BroncoSpace-BILLEE/BILLEE-Hardware-2025-2026/mercury-1/mercury-1.kicad_sch

## KiCad design mercury-1/mercury-1.kicad_sch (2026-02-26, an earlier design)

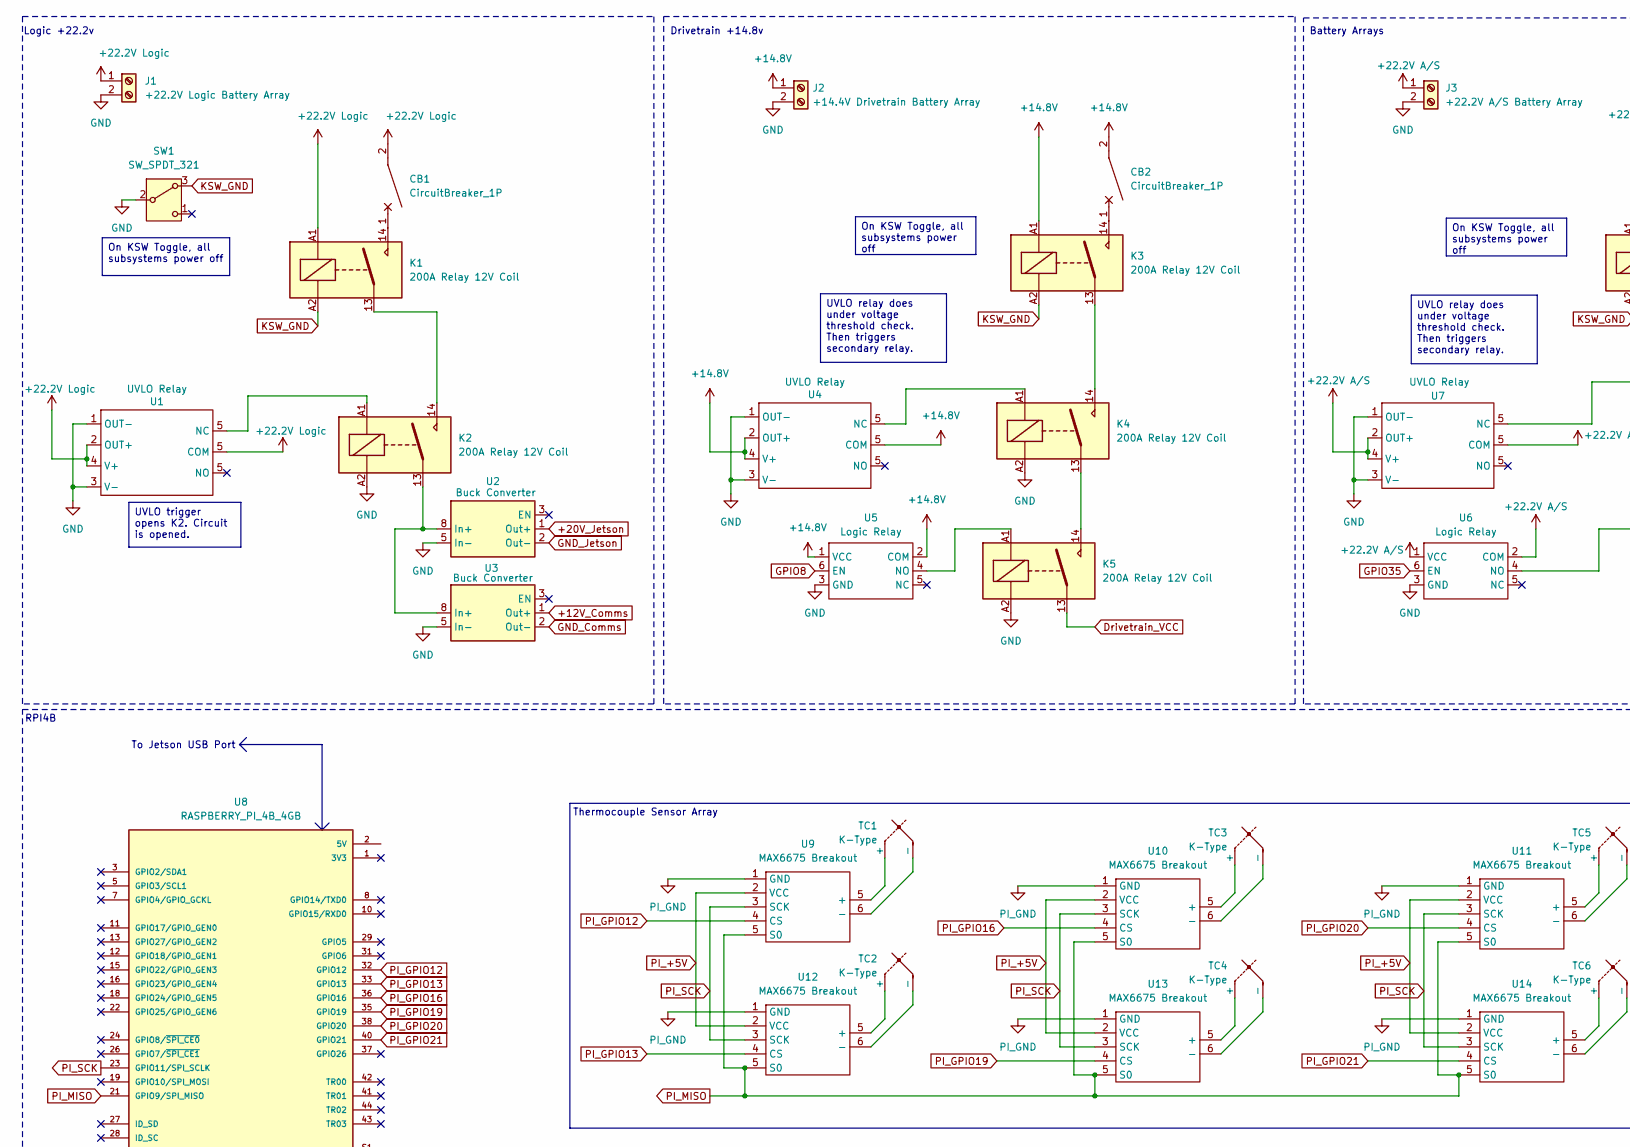
[picture p3: schematic mercury-1.kicad_sch, part in row 1, column 1]

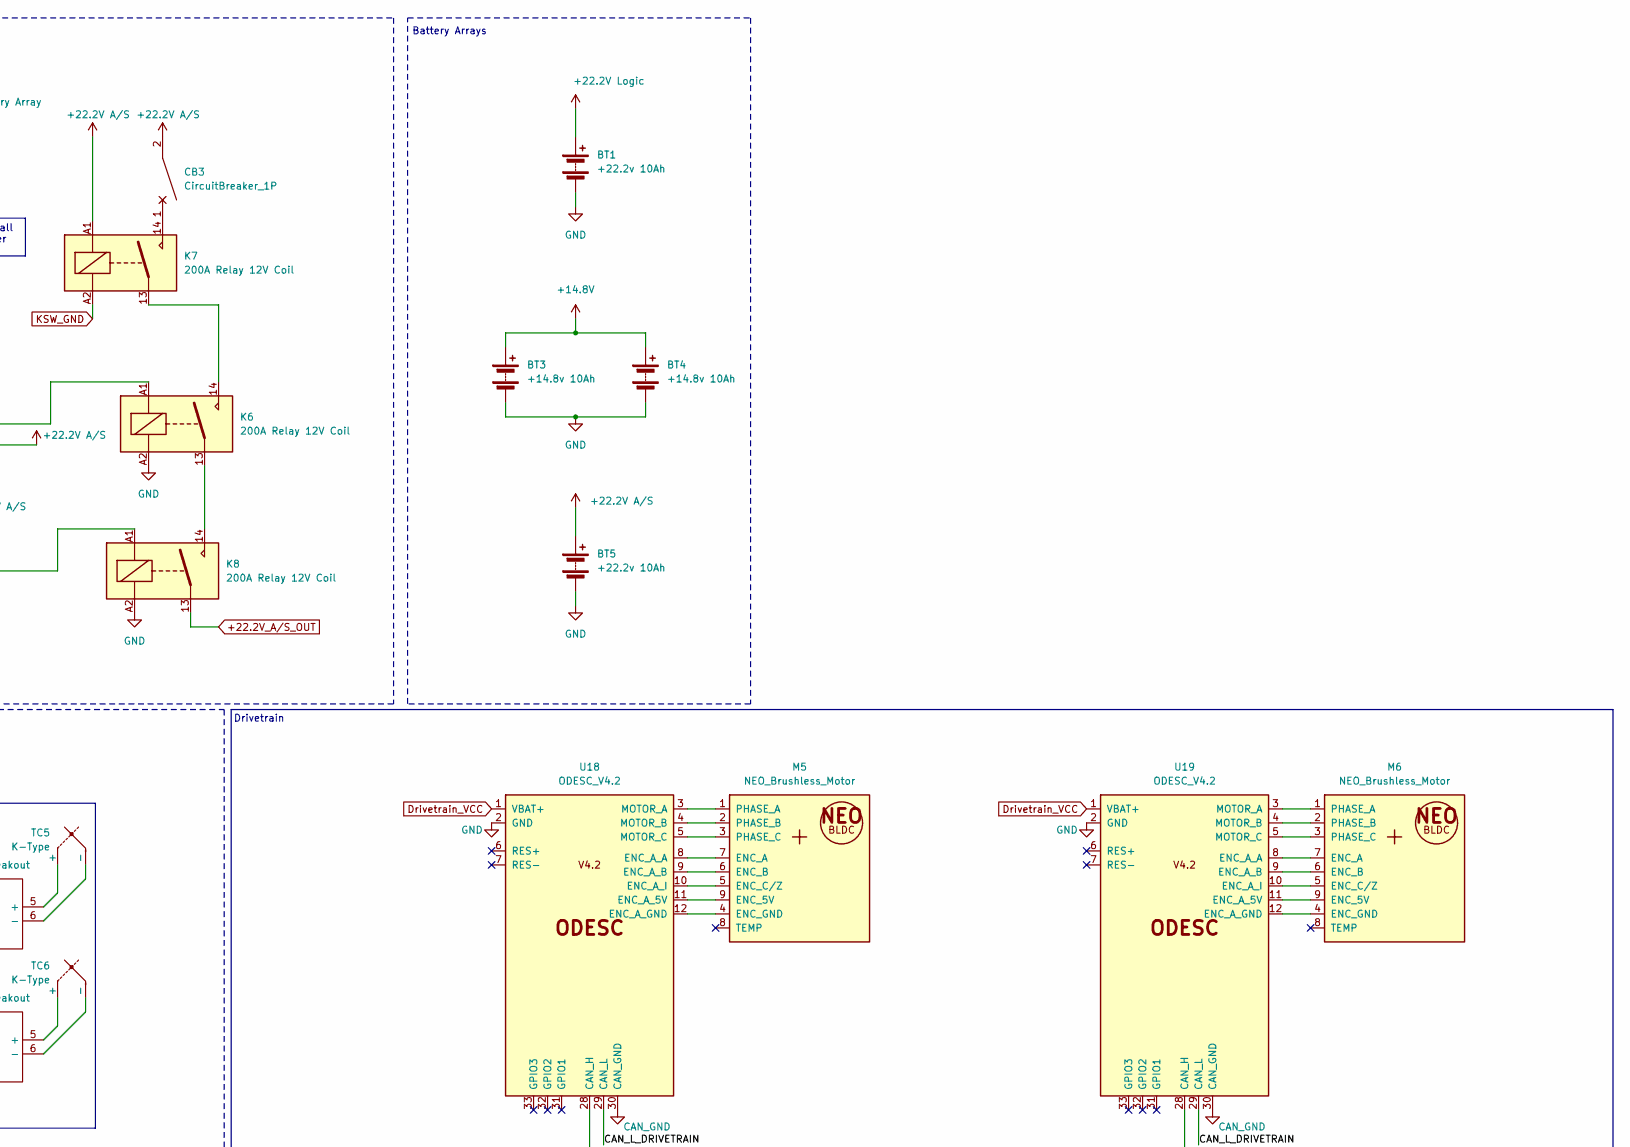
[picture p4: schematic mercury-1.kicad_sch, part in row 1, column 2]

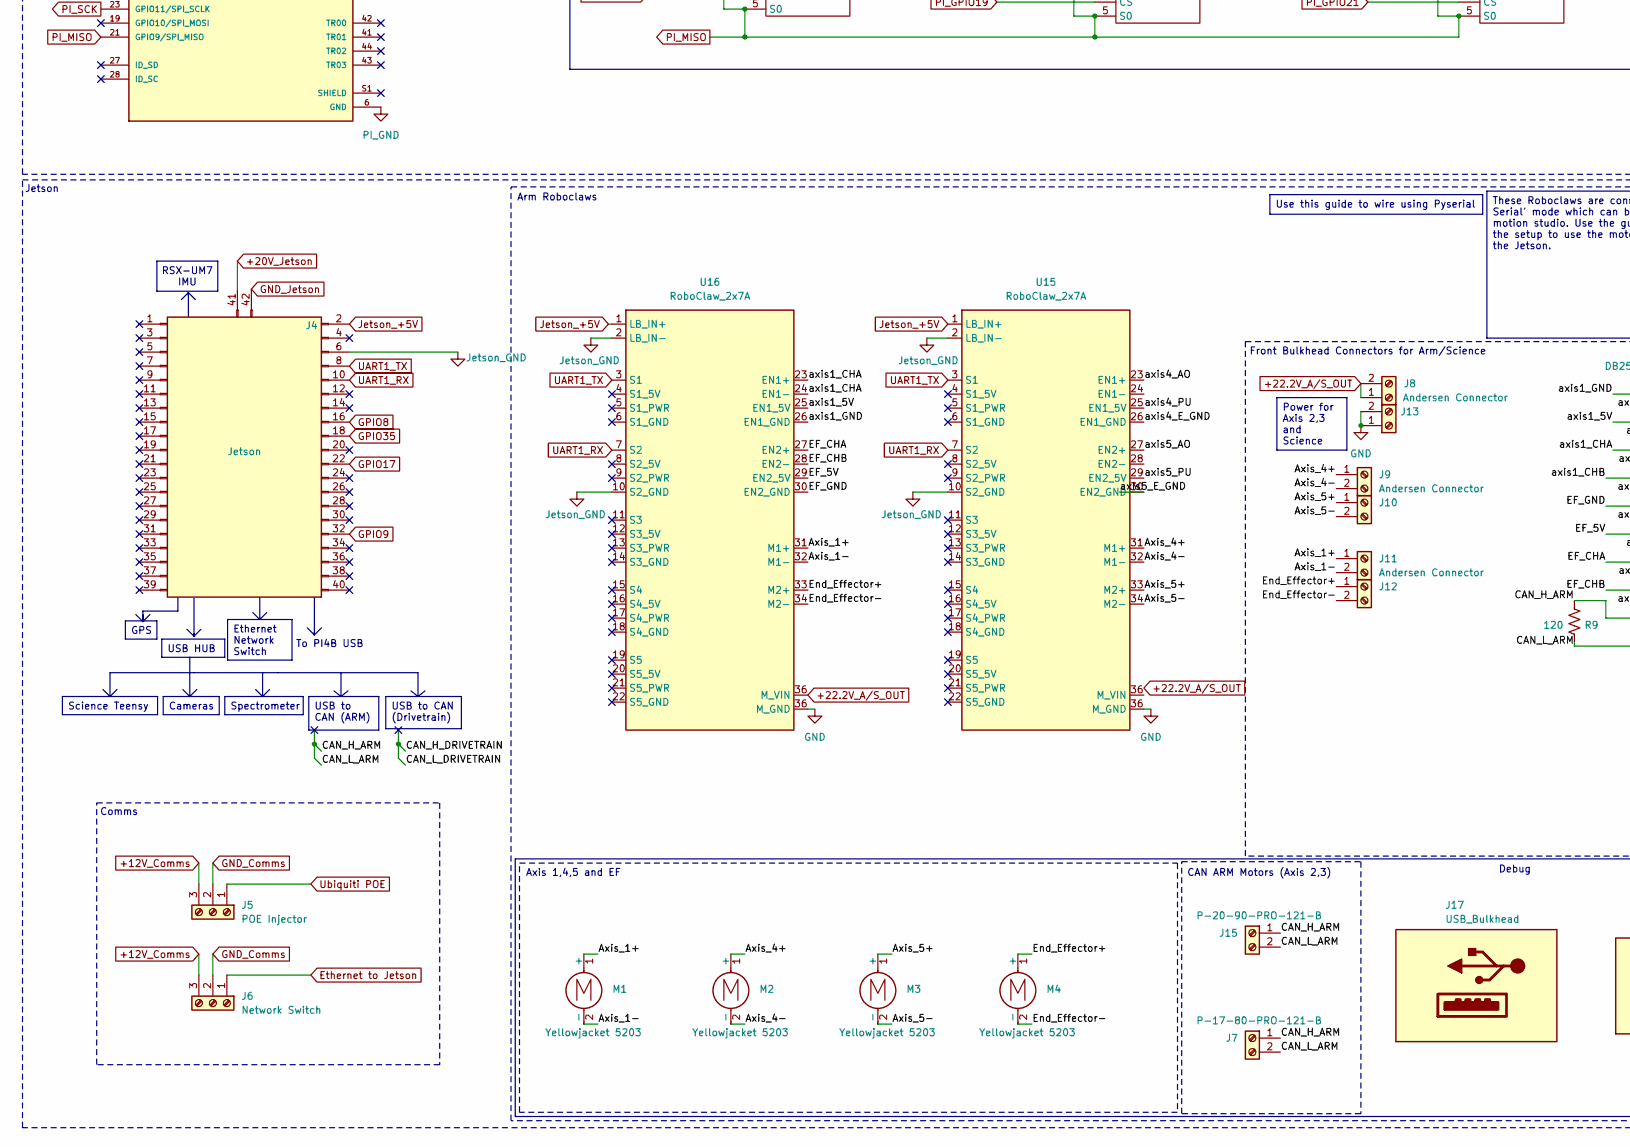
[picture p5: schematic mercury-1.kicad_sch, part in row 2, column 1]

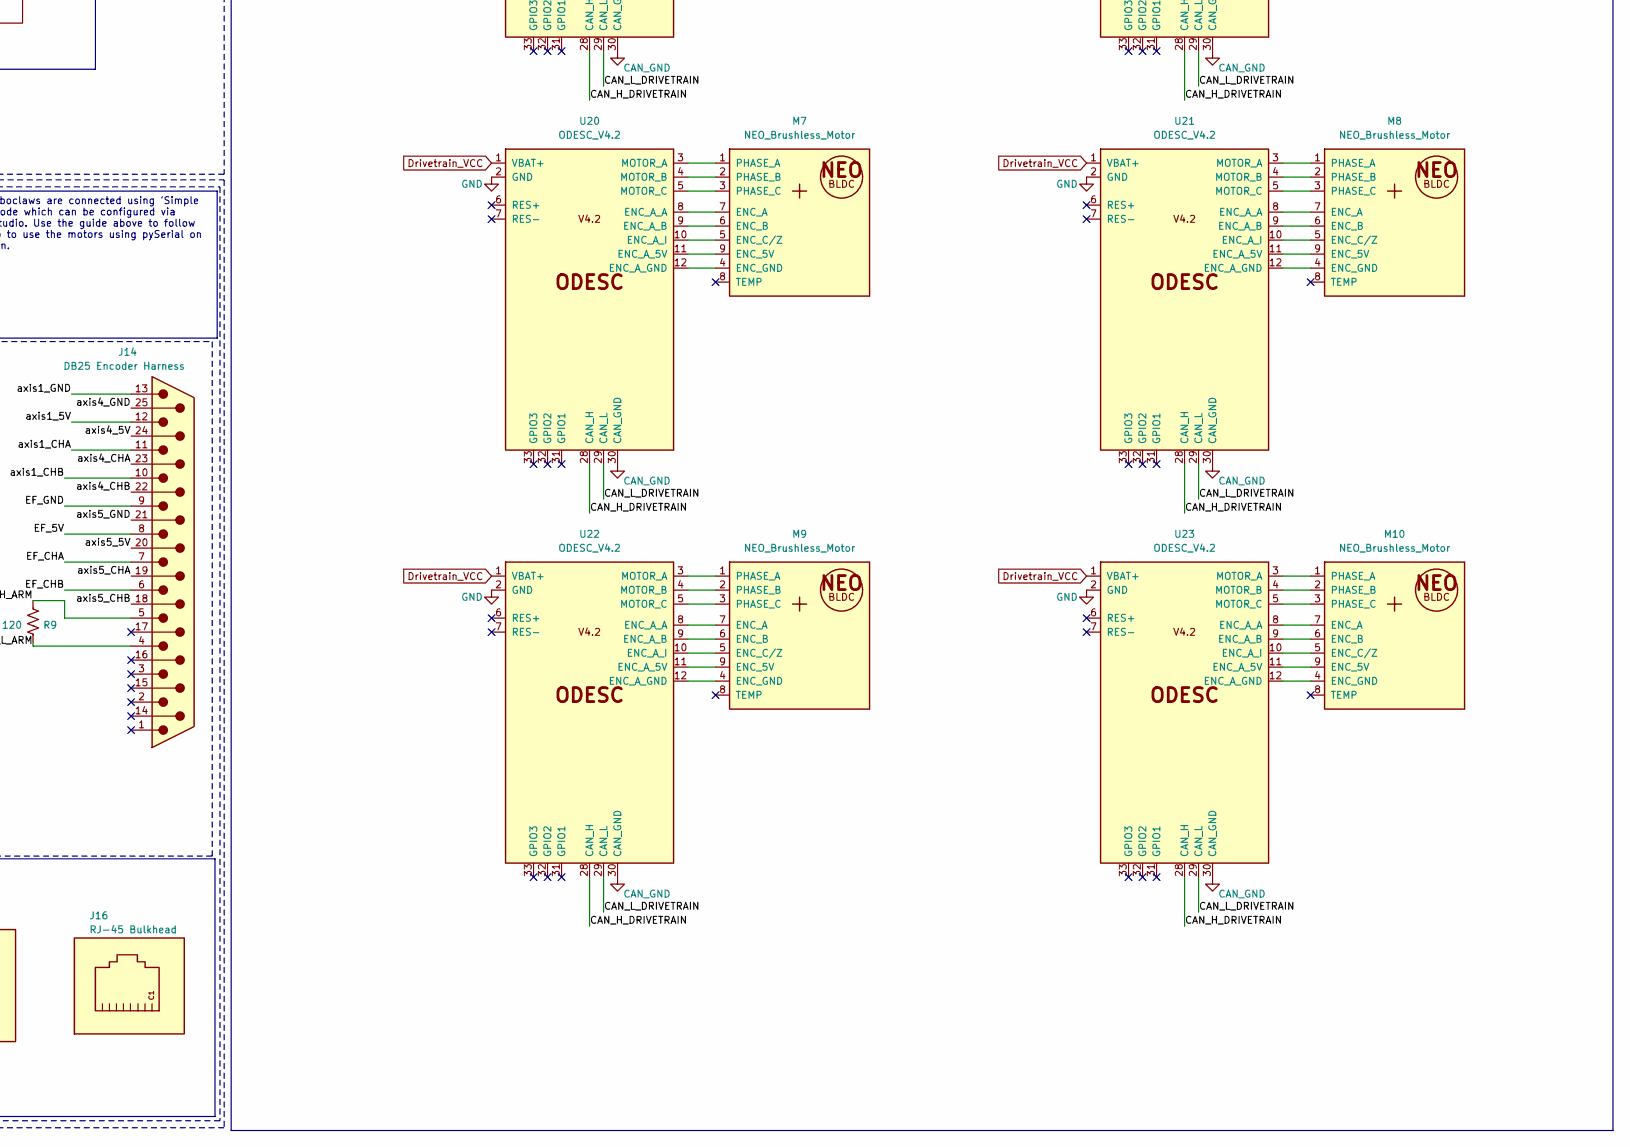
[picture p6: schematic mercury-1.kicad_sch, part in row 2, column 2]

Parts:
BT1, BT5: +22.2v 10Ah
BT3, BT4: +14.8v 10Ah
CB1, CB2, CB3: CircuitBreaker_1P
J1: +22.2V Logic Battery Array
J2: +14.4V Drivetrain Battery Array
J3: +22.2V A/S Battery Array
J4: Jetson
J5: POE Injector
J6: Network Switch
J7: P-17-80-PRO-121-B
J8, J9, J10, J11, J12, J13: Andersen Connector
J14: DB25 Encoder Harness
J15: P-20-90-PRO-121-B
J16: RJ-45 Bulkhead; RJ45_Bel_V895-1001-AW_Vertical
J17: USB_Bulkhead
K1, K2, K3, K4, K5, K6, K7, K8: 200A Relay 12V Coil
M1, M2, M3, M4: Yellowjacket 5203
M5, M6, M7, M8, M9, M10: NEO_Brushless_Motor
R9: 120
SW1: SW_SPDT_321
TC1, TC2, TC3, TC4, TC5, TC6: K-Type
U1, U4, U7: UVLO Relay
U2, U3: Buck Converter; HTSOP-8-1EP_3.9x4.9mm_P1.27mm_EP2.4x3.2mm
U5, U6: Logic Relay
U8: RASPBERRY_PI_4B_4GB; MODULE_RASPBERRY_PI_4B_4GB; PARTREV 4
U9, U10, U11, U12, U13, U14: MAX6675 Breakout
U15, U16: RoboClaw_2x7A
U18, U19, U20, U21, U22, U23: ODESC_V4.2

Connections:
+12V_Comms: J5.3, J6.3, U3.1 (Out+)
+14.8V: BT3.1 (+), BT4.1 (+), CB2.2, J2.1, K3.A1, U4.2 (OUT+), U4.4 (V+), U4.5 (NC), U5.1 (VCC), U5.2 (COM)
+20V_Jetson: J4.41, U2.1 (Out+)
+22.2V A/S: BT5.1 (+), CB3.2, J3.1, K7.A1, U6.1 (VCC), U6.2 (COM), U7.2 (OUT+), U7.4 (V+), U7.5 (NC)
+22.2V Logic: BT1.1 (+), CB1.2, J1.1, K1.A1, U1.2 (OUT+), U1.4 (V+), U1.5 (NC)
+22.2V_A/S_OUT: J8.1, J8.2, K8.13, U16.36 (M_VIN)
Axis_1+: J11.1, M1.1 (+), U16.31 (M1+)
Axis_1-: J11.2, M1.2 (-), U16.32 (M1-)
Axis_4+: J9.1, M2.1 (+), U15.31 (M1+)
Axis_4-: J9.2, M2.2 (-), U15.32 (M1-)
Axis_5+: J10.1, M3.1 (+), U15.33 (M2+)
Axis_5-: J10.2, M3.2 (-), U15.34 (M2-)
CAN_GND: U18.30 (CAN_GND), U19.30 (CAN_GND), U20.30 (CAN_GND), U21.30 (CAN_GND), U22.30 (CAN_GND), U23.30 (CAN_GND)
CAN_H_ARM: J7.1, J7.2, J14.4, J14.5, J15.1, J15.2, R9.1, R9.2
CAN_H_DRIVETRAIN: U18.28 (CAN_H), U18.29 (CAN_L), U19.28 (CAN_H), U19.29 (CAN_L), U20.28 (CAN_H), U20.29 (CAN_L), U21.28 (CAN_H), U21.29 (CAN_L), U22.28 (CAN_H), U22.29 (CAN_L), U23.28 (CAN_H), U23.29 (CAN_L)
Drivetrain_VCC: K5.13, U18.1 (VBAT+), U19.1 (VBAT+), U20.1 (VBAT+), U21.1 (VBAT+), U22.1 (VBAT+), U23.1 (VBAT+)
EF_5V: J14.8, U16.29 (EN2_5V)
EF_CHA: J14.7, U16.27 (EN2+)
EF_CHB: J14.6, U16.28 (EN2-)
EF_GND: J14.9, U16.30 (EN2_GND)
End_Effector+: J12.1, M4.1 (+), U16.33 (M2+)
End_Effector-: J12.2, M4.2 (-), U16.34 (M2-)
Ethernet to Jetson: J6.1
GND: BT1.2 (-), BT3.2 (-), BT4.2 (-), BT5.2 (-), J1.2, J2.2, J3.2, J13.1, J13.2, K2.A2, K4.A2, K5.A2, K6.A2, K8.A2, SW1.2 (B), U1.1 (OUT-), U1.3 (V-), U2.5 (In-), U3.5 (In-), U4.1 (OUT-), U4.3 (V-), U5.3 (GND), U6.3 (GND), U7.1 (OUT-), U7.3 (V-), U15.36 (M_VIN), U16.36 (M_VIN), U18.2 (GND), U19.2 (GND), U20.2 (GND), U21.2 (GND), U22.2 (GND), U23.2 (GND)
GND_Comms: J5.2, J6.2, U3.2 (Out-)
GND_Jetson: J4.42, U2.2 (Out-)
GPIO8: J4.16, U5.6 (EN)
GPIO9: J4.32
GPIO17: J4.22
GPIO35: J4.18, U6.6 (EN)
Jetson_+5V: J4.2, U15.1 (LB_IN+), U16.1 (LB_IN+)
Jetson_GND: J4.6, U15.2 (LB_IN-), U15.10 (S2_GND), U16.2 (LB_IN-), U16.10 (S2_GND)
KSW_GND: K1.A2, K3.A2, K7.A2, SW1.3 (A)
unnamed: CB1.1, K1.14
unnamed: CB2.1, K3.14
unnamed: CB3.1, K7.14
unnamed: K1.13, K2.14
unnamed: K2.13, U2.8 (In+), U3.8 (In+)
unnamed: K2.A1, U1.5 (NC)
unnamed: K3.13, K4.14
unnamed: K4.13, K5.14
unnamed: K4.A1, U4.5 (NC)
unnamed: K5.A1, U5.4 (NO)
unnamed: K6.13, K8.14
unnamed: K6.14, K7.13
unnamed: K6.A1, U7.5 (NC)
unnamed: K8.A1, U6.4 (NO)
unnamed: M5.1 (PHASE_A), U18.3 (MOTOR_A)
unnamed: M5.2 (PHASE_B), U18.4 (MOTOR_B)
unnamed: M5.3 (PHASE_C), U18.5 (MOTOR_C)
unnamed: M5.4 (ENC_GND), U18.12 (ENC_A_GND)
unnamed: M5.5 (ENC_C/Z), U18.10 (ENC_A_I)
unnamed: M5.6 (ENC_B), U18.9 (ENC_A_B)
unnamed: M5.7 (ENC_A), U18.8 (ENC_A_A)
unnamed: M5.9 (ENC_5V), U18.11 (ENC_A_5V)
unnamed: M6.1 (PHASE_A), U19.3 (MOTOR_A)
unnamed: M6.2 (PHASE_B), U19.4 (MOTOR_B)
unnamed: M6.3 (PHASE_C), U19.5 (MOTOR_C)
unnamed: M6.4 (ENC_GND), U19.12 (ENC_A_GND)
unnamed: M6.5 (ENC_C/Z), U19.10 (ENC_A_I)
unnamed: M6.6 (ENC_B), U19.9 (ENC_A_B)
unnamed: M6.7 (ENC_A), U19.8 (ENC_A_A)
unnamed: M6.9 (ENC_5V), U19.11 (ENC_A_5V)
unnamed: M7.1 (PHASE_A), U20.3 (MOTOR_A)
unnamed: M7.2 (PHASE_B), U20.4 (MOTOR_B)
unnamed: M7.3 (PHASE_C), U20.5 (MOTOR_C)
unnamed: M7.4 (ENC_GND), U20.12 (ENC_A_GND)
unnamed: M7.5 (ENC_C/Z), U20.10 (ENC_A_I)
unnamed: M7.6 (ENC_B), U20.9 (ENC_A_B)
unnamed: M7.7 (ENC_A), U20.8 (ENC_A_A)
unnamed: M7.9 (ENC_5V), U20.11 (ENC_A_5V)
unnamed: M8.1 (PHASE_A), U21.3 (MOTOR_A)
unnamed: M8.2 (PHASE_B), U21.4 (MOTOR_B)
unnamed: M8.3 (PHASE_C), U21.5 (MOTOR_C)
unnamed: M8.4 (ENC_GND), U21.12 (ENC_A_GND)
unnamed: M8.5 (ENC_C/Z), U21.10 (ENC_A_I)
unnamed: M8.6 (ENC_B), U21.9 (ENC_A_B)
unnamed: M8.7 (ENC_A), U21.8 (ENC_A_A)
unnamed: M8.9 (ENC_5V), U21.11 (ENC_A_5V)
unnamed: M9.1 (PHASE_A), U22.3 (MOTOR_A)
unnamed: M9.2 (PHASE_B), U22.4 (MOTOR_B)
unnamed: M9.3 (PHASE_C), U22.5 (MOTOR_C)
unnamed: M9.4 (ENC_GND), U22.12 (ENC_A_GND)
unnamed: M9.5 (ENC_C/Z), U22.10 (ENC_A_I)
unnamed: M9.6 (ENC_B), U22.9 (ENC_A_B)
unnamed: M9.7 (ENC_A), U22.8 (ENC_A_A)
unnamed: M9.9 (ENC_5V), U22.11 (ENC_A_5V)
unnamed: M10.1 (PHASE_A), U23.3 (MOTOR_A)
unnamed: M10.2 (PHASE_B), U23.4 (MOTOR_B)
unnamed: M10.3 (PHASE_C), U23.5 (MOTOR_C)
unnamed: M10.4 (ENC_GND), U23.12 (ENC_A_GND)
unnamed: M10.5 (ENC_C/Z), U23.10 (ENC_A_I)
unnamed: M10.6 (ENC_B), U23.9 (ENC_A_B)
unnamed: M10.7 (ENC_A), U23.8 (ENC_A_A)
unnamed: M10.9 (ENC_5V), U23.11 (ENC_A_5V)
unnamed: TC1.1 (+), U9.5 (S0)
unnamed: TC1.2 (-), U9.6 (-)
unnamed: TC2.1 (+), U12.5 (S0)
unnamed: TC2.2 (-), U12.6 (-)
unnamed: TC3.1 (+), U10.5 (S0)
unnamed: TC3.2 (-), U10.6 (-)
unnamed: TC4.1 (+), U13.5 (S0)
unnamed: TC4.2 (-), U13.6 (-)
unnamed: TC5.1 (+), U11.5 (S0)
unnamed: TC5.2 (-), U11.6 (-)
unnamed: TC6.1 (+), U14.5 (S0)
unnamed: TC6.2 (-), U14.6 (-)
unnamed: U2.4 (GND), U2.6 (GND), U2.7 (GND), U2.9 (GND)
unnamed: U3.4 (GND), U3.6 (GND), U3.7 (GND), U3.9 (GND)
unnamed: U8.1 (3V3), U8.17 (3V3)
unnamed: U8.2 (5V), U8.4 (5V)
unnamed: U8.S1 (SHIELD), U8.S2 (SHIELD), U8.S3 (SHIELD), U8.S4 (SHIELD)
PI_+5V: U9.2 (VCC), U10.2 (VCC), U11.2 (VCC), U12.2 (VCC), U13.2 (VCC), U14.2 (VCC)
PI_GND: U8.6 (GND), U8.9 (GND), U8.14 (GND), U8.20 (GND), U8.25 (GND), U8.30 (GND), U8.34 (GND), U8.39 (GND), U9.1 (GND), U10.1 (GND), U11.1 (GND), U12.1 (GND), U13.1 (GND), U14.1 (GND)
PI_GPIO12: U8.32 (GPIO12), U9.4 (CS)
PI_GPIO13: U8.33 (GPIO13), U12.4 (CS)
PI_GPIO16: U8.36 (GPIO16), U10.4 (CS)
PI_GPIO19: U8.35 (GPIO19), U13.4 (CS)
PI_GPIO20: U8.38 (GPIO20), U11.4 (CS)
PI_GPIO21: U8.40 (GPIO21), U14.4 (CS)
PI_MISO: U8.21 (GPIO9/SPI_MISO), U9.5 (S0), U10.5 (S0), U11.5 (S0), U12.5 (S0), U13.5 (S0), U14.5 (S0)
PI_SCK: U8.23 (GPIO11/SPI_SCLK), U9.3 (SCK), U10.3 (SCK), U11.3 (SCK), U12.3 (SCK), U13.3 (SCK), U14.3 (SCK)
UART1_RX: J4.10, U15.7 (S2), U16.7 (S2)
UART1_TX: J4.8, U15.3 (S1), U16.3 (S1)
Ubiquiti POE: J5.1
axis1_5V: J14.12, U16.25 (EN1_5V)
axis1_CHA: J14.11, U16.23 (EN1+), U16.24 (EN1-)
axis1_CHB: J14.10
axis1_GND: J14.13, U16.26 (EN1_GND)
axis4_5V: J14.24
axis4_AO: U15.23 (EN1+)
axis4_CHA: J14.23
axis4_CHB: J14.22
axis4_E_GND: U15.26 (EN1_GND)
axis4_GND: J14.25
axis4_PU: U15.25 (EN1_5V)
axis5_5V: J14.20
axis5_AO: U15.27 (EN2+)
axis5_CHA: J14.19
axis5_CHB: J14.18
axis5_E_GND: U15.30 (EN2_GND)
axis5_GND: J14.21
axis5_PU: U15.29 (EN2_5V)

Notes on the sheet:
To PI4B USB
Battery Arrays
Debug
Comms
CAN ARM Motors (Axis 2,3)
Axis 1,4,5 and EF
To Jetson USB Port
Thermocouple Sensor Array
Jetson
Drivetrain
Logic +22.2v
Drivetrain +14.8v
RPI4B
Front Bulkhead Connectors for Arm/Science
Arm Roboclaws
On KSW Toggle, all subsystems power off
Spectrometer
UVLO trigger opens K2. Circuit is opened.
RSX-UM7 IMU
USB to CAN (Drivetrain)
UVLO relay does under voltage threshold check. Then triggers secondary relay.
Ethernet Network Switch
USB HUB
GPS
Power for Axis 2,3 and Science
These Roboclaws are connected using 'Simple Serial' mode which can be configured via motion studio. Use the guide above to follow the setup to use the motors using pySerial on the Jetson.
Cameras
Science Teensy
Use this guide to wire using Pyserial
USB to CAN (ARM)
