BroncoSpace-BILLEE/BILLEE-Hardware-2025-2026/mercury-1/science.kicad_sch

## KiCad design mercury-1/science.kicad_sch (2026-02-27, an earlier design)

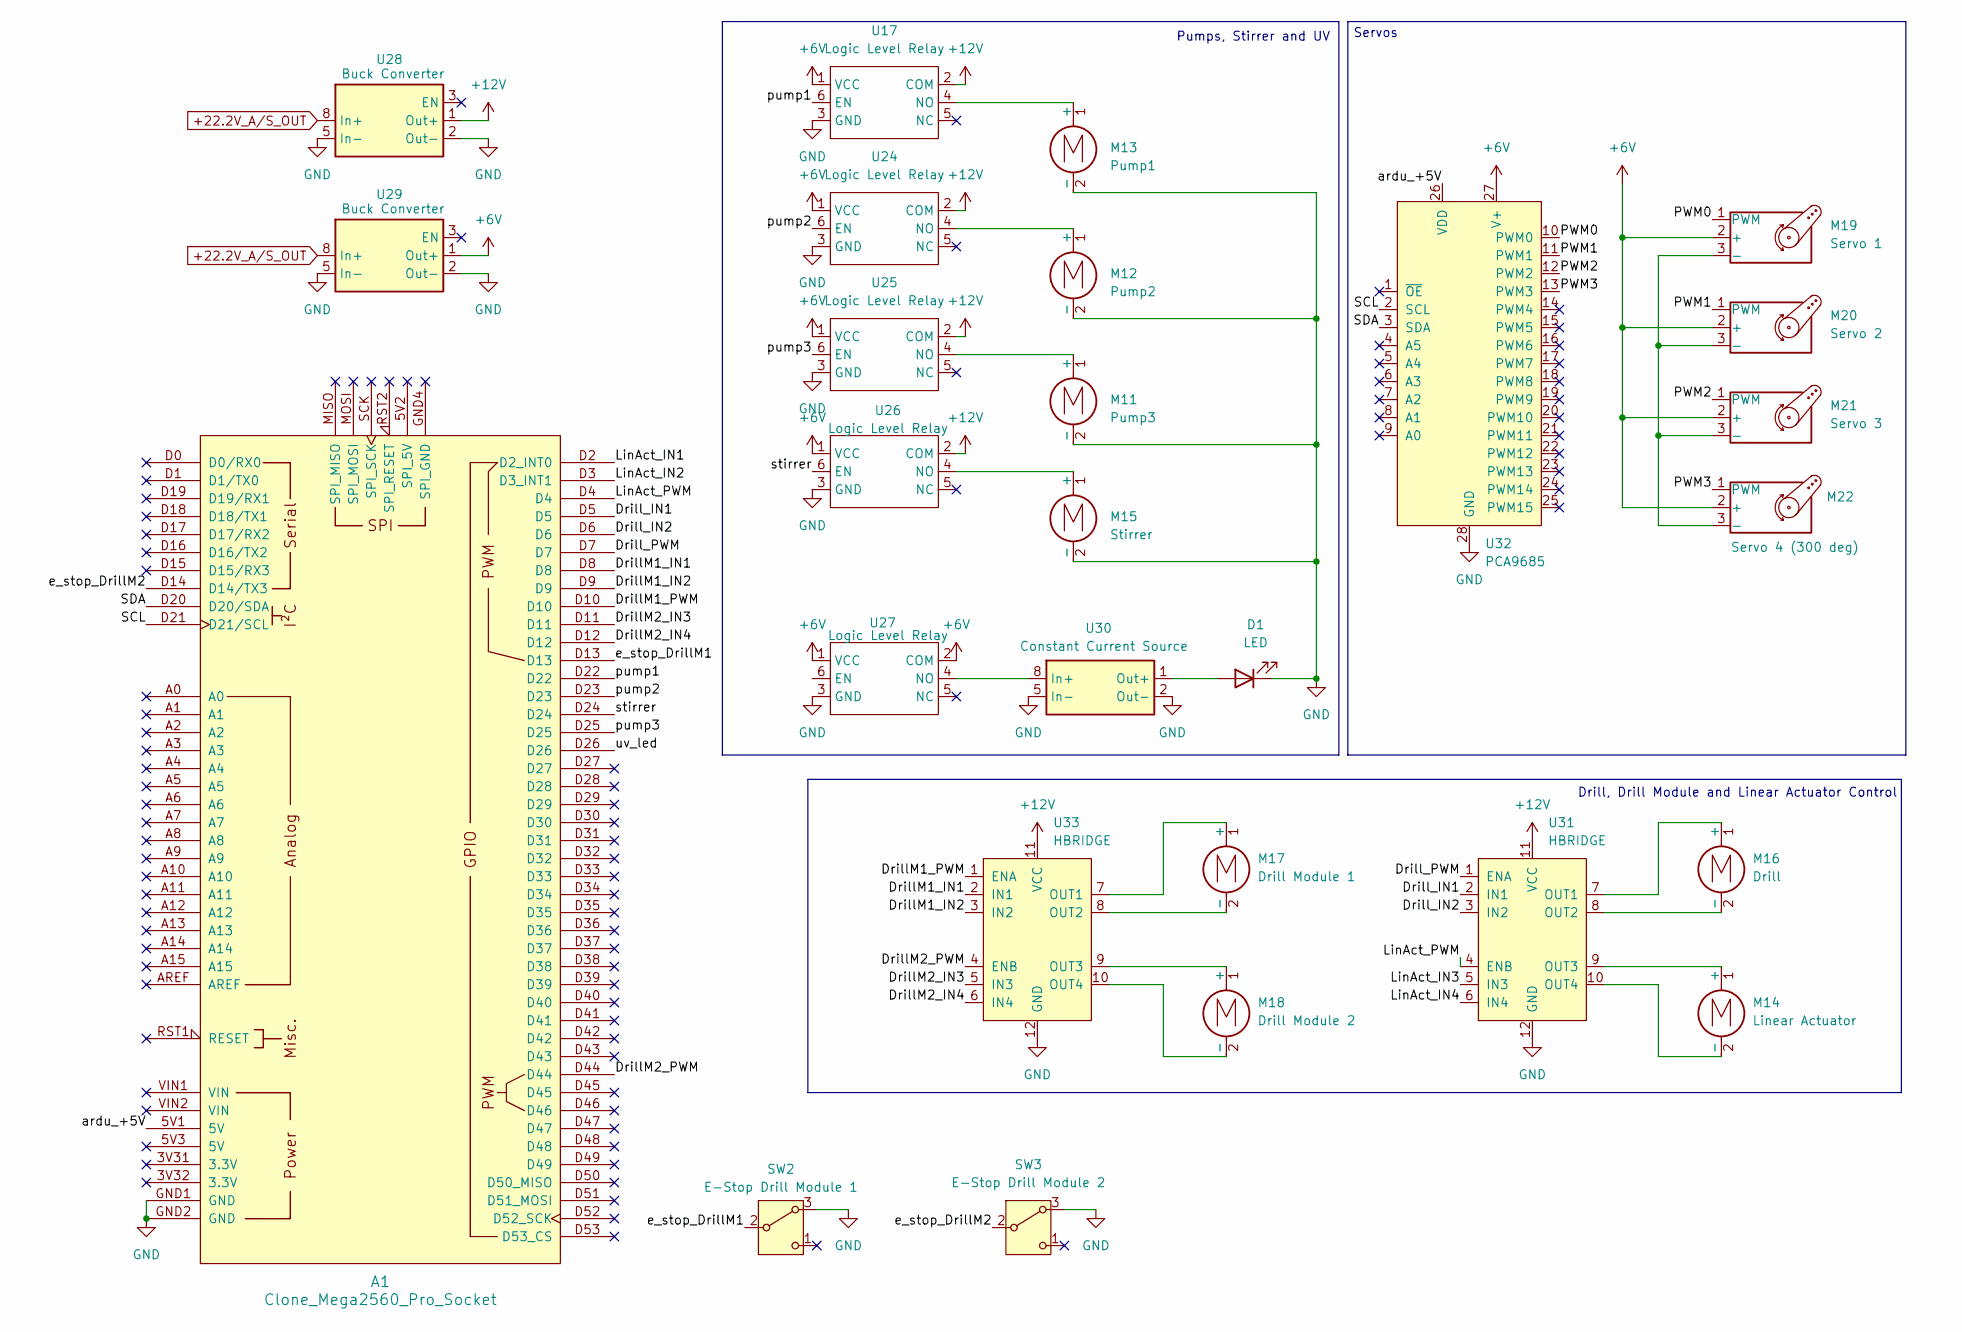
[picture p7: schematic science.kicad_sch]

Parts:
A1: Clone_Mega2560_Pro_Socket
D1: LED
M11: Pump3
M12: Pump2
M13: Pump1
M14: Linear Actuator
M15: Stirrer
M16: Drill
M17: Drill Module 1
M18: Drill Module 2
M19: Servo 1
M20: Servo 2
M21: Servo 3
M22: Servo 4 (300 deg)
SW2: E-Stop Drill Module 1; Nidec_Copal_CAS-120A
SW3: E-Stop Drill Module 2; Nidec_Copal_CAS-120A
U17, U24, U25, U26, U27: Logic Level Relay
U28, U29: Buck Converter; HTSOP-8-1EP_3.9x4.9mm_P1.27mm_EP2.4x3.2mm
U30: Constant Current Source; HTSOP-8-1EP_3.9x4.9mm_P1.27mm_EP2.4x3.2mm
U31, U33: HBRIDGE
U32: PCA9685; SSOP-28_5.3x10.2mm_P0.65mm

Connections:
+6V: M19.2 (+), M20.2 (+), M21.2 (+), M22.2 (+), U17.1 (VCC), U24.1 (VCC), U25.1 (VCC), U26.1 (VCC), U27.1 (VCC), U27.2 (COM), U29.1 (Out+), U32.27 (V+)
+12V: U17.2 (COM), U24.2 (COM), U25.2 (COM), U26.2 (COM), U28.1 (Out+), U31.11 (VCC), U33.11 (VCC)
+22.2V_A/S_OUT: U28.8 (In+), U29.8 (In+)
DrillM1_IN1: A1.D8, U33.2 (IN1)
DrillM1_IN2: A1.D9, U33.3 (IN2)
DrillM1_PWM: A1.D10, U33.1 (ENA)
DrillM2_IN3: A1.D11, U33.5 (IN3)
DrillM2_IN4: A1.D12, U33.6 (IN4)
DrillM2_PWM: A1.D44, U33.4 (ENB)
Drill_IN1: A1.D5, U31.2 (IN1)
Drill_IN2: A1.D6, U31.3 (IN2)
Drill_PWM: A1.D7, U31.1 (ENA)
GND: A1.GND1 (GND), A1.GND2 (GND), D1.1 (K), M11.2 (-), M12.2 (-), M13.2 (-), M15.2 (-), SW2.3 (A), SW3.3 (A), U17.3 (GND), U24.3 (GND), U25.3 (GND), U26.3 (GND), U27.3 (GND), U28.2 (Out-), U28.5 (In-), U29.2 (Out-), U29.5 (In-), U30.2 (Out-), U30.5 (In-), U31.12 (GND), U32.28 (GND), U33.12 (GND)
LinAct_IN1: A1.D2 (D2_INT0)
LinAct_IN2: A1.D3 (D3_INT1)
LinAct_IN3: U31.5 (IN3)
LinAct_IN4: U31.6 (IN4)
LinAct_PWM: A1.D4, U31.4 (ENB)
unnamed: D1.2 (A), U30.1 (Out+)
unnamed: M11.1 (+), U25.4 (NO)
unnamed: M12.1 (+), U24.4 (NO)
unnamed: M13.1 (+), U17.4 (NO)
unnamed: M14.1 (+), U31.9 (OUT3)
unnamed: M14.2 (-), U31.10 (OUT4)
unnamed: M15.1 (+), U26.4 (NO)
unnamed: M16.1 (+), U31.7 (OUT1)
unnamed: M16.2 (-), U31.8 (OUT2)
unnamed: M17.1 (+), U33.7 (OUT1)
unnamed: M17.2 (-), U33.8 (OUT2)
unnamed: M18.1 (+), U33.9 (OUT3)
unnamed: M18.2 (-), U33.10 (OUT4)
unnamed: M19.3 (-), M20.3 (-), M21.3 (-), M22.3 (-)
unnamed: U27.4 (NO), U30.8 (In+)
unnamed: U28.4 (GND), U28.6 (GND), U28.7 (GND), U28.9 (GND)
unnamed: U29.4 (GND), U29.6 (GND), U29.7 (GND), U29.9 (GND)
unnamed: U30.4 (GND), U30.6 (GND), U30.7 (GND), U30.9 (GND)
PWM0: M19.1 (PWM), U32.10 (PWM0)
PWM1: M20.1 (PWM), U32.11 (PWM1)
PWM2: M21.1 (PWM), U32.12 (PWM2)
PWM3: M22.1 (PWM), U32.13 (PWM3)
SCL: A1.D21 (D21/SCL), U32.2 (SCL)
SDA: A1.D20 (D20/SDA), U32.3 (SDA)
ardu_+5V: A1.5V1 (5V), U32.26 (VDD)
e_stop_DrillM1: A1.D13, SW2.2 (B)
e_stop_DrillM2: A1.D14 (D14/TX3), SW3.2 (B)
pump1: A1.D22, U17.6 (EN)
pump2: A1.D23, U24.6 (EN)
pump3: A1.D25, U25.6 (EN)
stirrer: A1.D24, U26.6 (EN)
uv_led: A1.D26

Notes on the sheet:
Servos
Drill, Drill Module and Linear Actuator Control
Pumps, Stirrer and UV
