BroncoSpace-BILLEE/BILLEE-Hardware-2025-2026/mercury-1/mercury-1/power.kicad_sch

## KiCad design mercury-1/mercury-1/power.kicad_sch (2026-01-27)

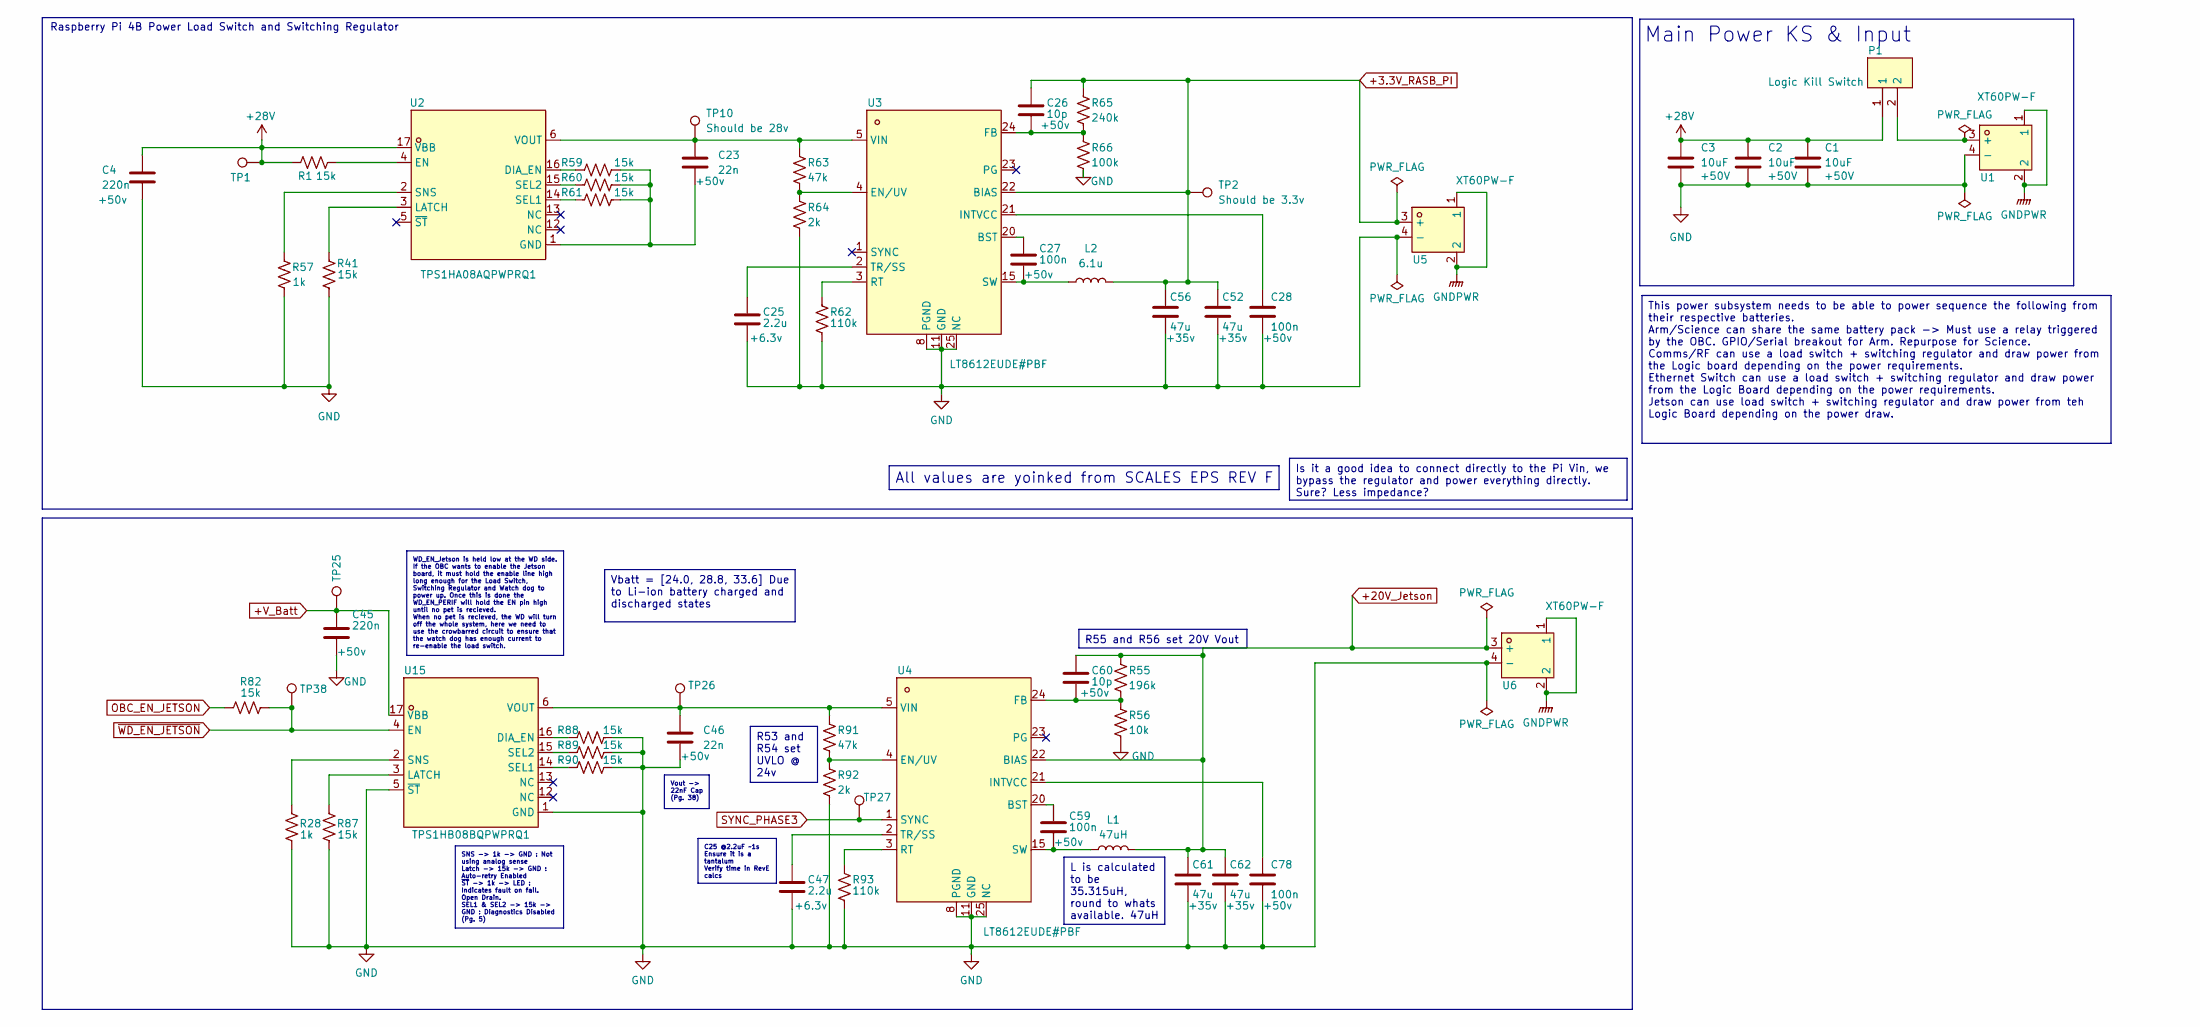
[picture p8: schematic power.kicad_sch]

Parts:
C1, C2, C3: 10uF; Voltage +50V
C4, C45: 220n; C0402; Voltage Rating +50v; LCSC C5159775
C23, C46: 22n; C0402; Voltage Rating +50v; LCSC C77023
C25, C47: 2.2u; C0402; Voltage Rating +6.3v; LCSC C12530
C26, C60: 10p; C0402; Voltage Rating +50v; LCSC C1545
C27, C28, C59, C78: 100n; C0402; Voltage Rating +50v; LCSC C85858
C52, C56, C61, C62: 47u; CAP-SMD_L7.3-W4.3-FD; Voltage Rating +35v; LCSC C87110
L1: 47uH; IND-SMD_L10.7-W10.0_ETQP5MXXXX; LCSC C409637
L2: 6.1u; IND-SMD_FTKB1207-6R1NT; LCSC C3040409
P1: Logic Kill Switch; CONN-TH_2P-P5.00_WJ500V-5.08-2P; LCSC Part C8465
R1: 15k; R0402; LCSC C106235
R28, R57: 1k; R0402; LCSC C106235
R41, R82, R87, R88, R89, R90: 15k; R0402; LCSC C114761
R55: 196k; R0402; LCSC C2077051
R56: 10k; R0402; LCSC C25531
R59, R60, R61: 15k; R0402; LCSC C25756
R62, R93: 110k; R0402; LCSC C138065
R63, R91: 47k; R0402; LCSC C93943
R64, R92: 2k; R0402; LCSC C60488
R65: 240k; R0402; LCSC C138029
R66: 100k; R0402; LCSC C60491
TP1, TP25, TP26, TP27, TP38: TestPoint; TestPoint_Pad_1.0x1.0mm
TP2: Should be 3.3v; TestPoint_Pad_1.0x1.0mm
TP10: Should be 28v; TestPoint_Pad_1.0x1.0mm
U1, U5, U6: XT60PW-F; TH_2P-XT60PW-F; LCSC Part C428722
U2: TPS1HA08AQPWPRQ1; HTSSOP-16_L5.0-W4.4-P0.65-LS6.4-BL-EP; LCSC Part C3230076
U3, U4: LT8612EUDE#PBF; QFN-28_L6.0-W3.0-P0.50-BL-EP; LCSC Part C580312
U15: TPS1HB08BQPWPRQ1; HTSSOP-16_L5.0-W4.4-P0.65-LS6.4-TL-EP2.9; LCSC Part C3230075

Connections:
+3.3V_RASB_PI: C26.1, C52.1, C56.1, L2.2, R65.1, TP2.1, U3.22 (BIAS), U5.3 (+)
+20V_Jetson: C60.1, C61.1, C62.1, L1.2, R55.1, U4.22 (BIAS), U6.3 (+)
+28V: C1.1, C2.1, C3.1, C4.1, P1.1, R1.2, TP1.1, U2.17 (VBB)
+V_Batt: C45.1, TP25.1, U15.17 (VBB)
GND: C1.2, C2.2, C3.2, C4.2, C25.2, C28.2, C45.2, C46.2, C47.2, C52.2, C56.2, C61.2, C62.2, C78.2, R28.1, R41.1, R56.2, R57.1, R62.2, R64.2, R66.2, R87.2, R88.2, R89.2, R90.2, R92.2, R93.2, U1.4 (-), U3.8 (PGND), U3.11 (GND), U3.25 (NC), U4.8 (PGND), U4.11 (GND), U4.25 (NC), U5.4 (-), U6.4 (-), U15.1 (GND), U15.5 (~ST)
GNDPWR: U1.1, U1.2, U5.1, U5.2, U6.1, U6.2
unnamed: C23.1, R63.1, TP10.1, U2.6 (VOUT), U3.5 (VIN)
unnamed: C23.2, R59.2, R60.2, R61.2, U2.1 (GND)
unnamed: C25.1, U3.2 (TR/SS)
unnamed: C26.2, R65.2, R66.1, U3.24 (FB)
unnamed: C27.1, U3.20 (BST)
unnamed: C27.2, L2.1, U3.15 (SW)
unnamed: C28.1, U3.21 (INTVCC)
unnamed: C46.1, R91.1, TP26.1, U4.5 (VIN), U15.6 (VOUT)
unnamed: C47.1, U4.2 (TR/SS)
unnamed: C59.1, U4.20 (BST)
unnamed: C59.2, L1.1, U4.15 (SW)
unnamed: C60.2, R55.2, R56.1, U4.24 (FB)
unnamed: C78.1, U4.21 (INTVCC)
unnamed: P1.2, U1.3 (+)
unnamed: R1.1, U2.4 (EN)
unnamed: R28.2, U15.2 (SNS)
unnamed: R41.2, U2.3 (LATCH)
unnamed: R57.2, U2.2 (SNS)
unnamed: R59.1, U2.16 (DIA_EN)
unnamed: R60.1, U2.15 (SEL2)
unnamed: R61.1, U2.14 (SEL1)
unnamed: R62.1, U3.3 (RT)
unnamed: R63.2, R64.1, U3.4 (EN/UV)
unnamed: R87.1, U15.3 (LATCH)
unnamed: R88.1, U15.16 (DIA_EN)
unnamed: R89.1, U15.15 (SEL2)
unnamed: R90.1, U15.14 (SEL1)
unnamed: R91.2, R92.1, U4.4 (EN/UV)
unnamed: R93.1, U4.3 (RT)
OBC_EN_JETSON: R82.2
SYNC_PHASE3: TP27.1, U4.1 (SYNC)
~WD_EN_JETSON: R82.1, TP38.1, U15.4 (EN)

Notes on the sheet:
Raspberry Pi 4B Power Load Switch and Switching Regulator
Main Power KS & Input
Is it a good idea to connect directly to the Pi Vin, we bypass the regulator and power everything directly. Sure? Less impedance?
SNS -> 1k -> GND : Not using analog sense Latch -> 15k -> GND : Auto-retry Enabled ~{ST} -> 1k -> LED : Indicates fault on fail. Open Drain. SEL1 & SEL2 -> 15k -> GND : Diagnostics Disabled (Pg. 5)
Vout -> 22nF Cap (Pg. 38)
All values are yoinked from SCALES EPS REV F
R53 and R54 set UVLO @ 24v
WD_EN_Jetson is held low at the WD side. If the OBC wants to enable the Jetson board, it must hold the enable line high long enough for the Load Switch, Switching Regulator and Watch dog to power up. Once this is done the WD_EN_PERIF will hold the EN pin high until no pet is recieved. When no pet i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
Vbatt = [24.0, 28.8, 33.6] Due to Li-ion battery charged and discharged states
R55 and R56 set 20V Vout
C25 @2.2uF ~1s Ensure it is a tantalum Verify time in RevE calcs
This power subsystem needs to be able to power sequence the following from their respective batteries. Arm/Science can share the same battery pack -> Must use a relay triggered by the OBC. GPIO/Serial breakout for Arm. Repurpose for Science. Comms/RF can use a load switch + switching regulator and 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
L is calculated to be 35.315uH, round to whats available. 47uH
